jeremygustafson/WarpCore/warp_core_audio/main/Config.h

/*
 * Config.h
 *
 *  Created on: 22 Feb 2018
 *      Author: dancl
 */

#ifndef MAIN_CONFIG_H_
#define MAIN_CONFIG_H_

#define PIN_I2S_LRC			(18)
#define PIN_I2S_BCLK		(23)
#define PIN_I2S_DATA		(19)

#define PIN_UART_RX			(26)
#define PIN_UART_TX			(27)

#endif /* MAIN_CONFIG_H_ */
