jeremygustafson/WarpCore/warp_core/main/animations/colour.h

/*
 * colour.h
 *
 *  Created on: 9 Mar 2018
 *      Author: dancl
 */

#ifndef MAIN_ANIMATIONS_COLOUR_H_
#define MAIN_ANIMATIONS_COLOUR_H_

#include "WarpCoreVisual.h"

led_t getRgbColour(uint8_t wheelPos);

#endif /* MAIN_ANIMATIONS_COLOUR_H_ */
