jeremygustafson/WarpCore/warp_core_audio/main/AudioFiles.h

/*
 * AudioFiles.h
 *
 *  Created on: 23 Feb 2018
 *      Author: dancl
 */

#ifndef MAIN_AUDIOFILES_H_
#define MAIN_AUDIOFILES_H_

extern const unsigned char redalert_wav_start[] asm("_binary_redalert_wav_start");
extern const unsigned char redalert_wav_end[]   asm("_binary_redalert_wav_end");

extern const unsigned char redalert_vgr_wav_start[] asm("_binary_redalert_vgr_wav_start");
extern const unsigned char redalert_vgr_wav_end[]   asm("_binary_redalert_vgr_wav_end");

extern const unsigned char core_wav_start[] asm("_binary_core_wav_start");
extern const unsigned char core_wav_end[] asm("_binary_core_wav_end");

extern const unsigned char core_max_wav_start[] asm("_binary_core_max_wav_start");
extern const unsigned char core_max_wav_end[]   asm("_binary_core_max_wav_end");

extern const unsigned char breach_wav_start[] asm("_binary_breach_wav_start");
extern const unsigned char breach_wav_end[] asm("_binary_breach_wav_end");

#endif /* MAIN_AUDIOFILES_H_ */
